KylianAlgoet/Sk8Sense/docs/magazine/screenshots/01_home.png

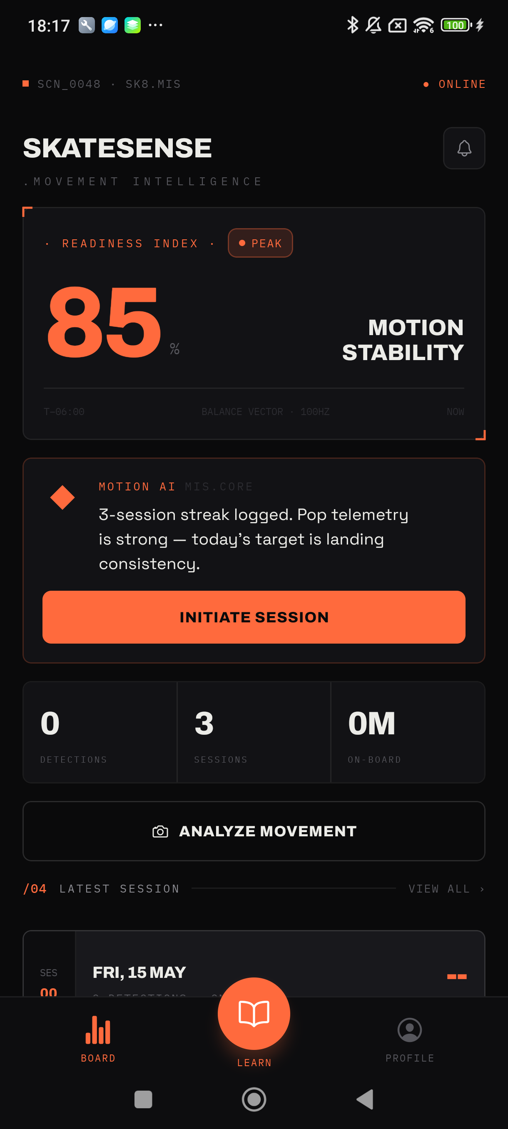
docs/magazine/screenshots/01_home.png
